The8BitEnthusiast/apple-1-breadboard/schematics/aci.kicad_sch

## KiCad design schematics/aci.kicad_sch (2024-11-09, an earlier design)

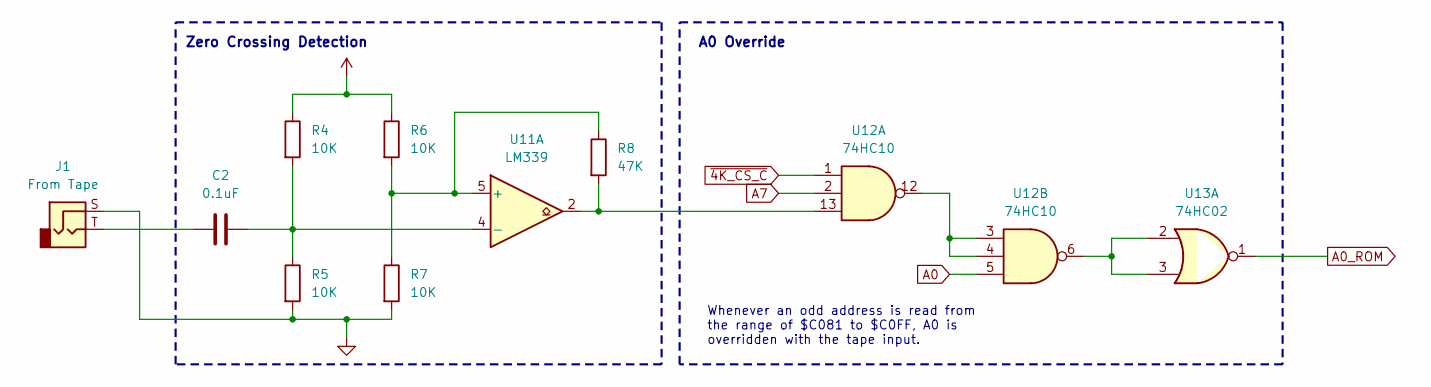
[picture p7: schematic aci.kicad_sch]

Parts:
C2: 0.1uF
J1: From Tape
R4, R5, R6, R7: 10K
R8: 47K
U11: LM339
U12: 74HC10
U13: 74HC02

Connections:
A0: U12.5
A0_ROM: U13.1
A7: U12.2
GND: J1.S, R5.2, R7.2
unnamed: C2.1, J1.T
unnamed: C2.2, R4.2, R5.1, U11.4 (-)
unnamed: R6.2, R7.1, R8.1, U11.5 (+)
unnamed: R8.2, U11.2, U12.13
unnamed: U12.6, U13.2, U13.3
unnamed: U12.3, U12.4, U12.12
VCC: R4.1, R6.1
~4K_CS_C: U12.1

Notes on the sheet:
A0 Override
Whenever an odd address is read from the range of $C081 to $C0FF, A0 is overridden with the tape input.
Zero Crossing Detection
