The8BitEnthusiast/apple-1-breadboard/schematics/apple-1.kicad_sch

## KiCad design schematics/apple-1.kicad_sch (2025-04-07, an earlier design)

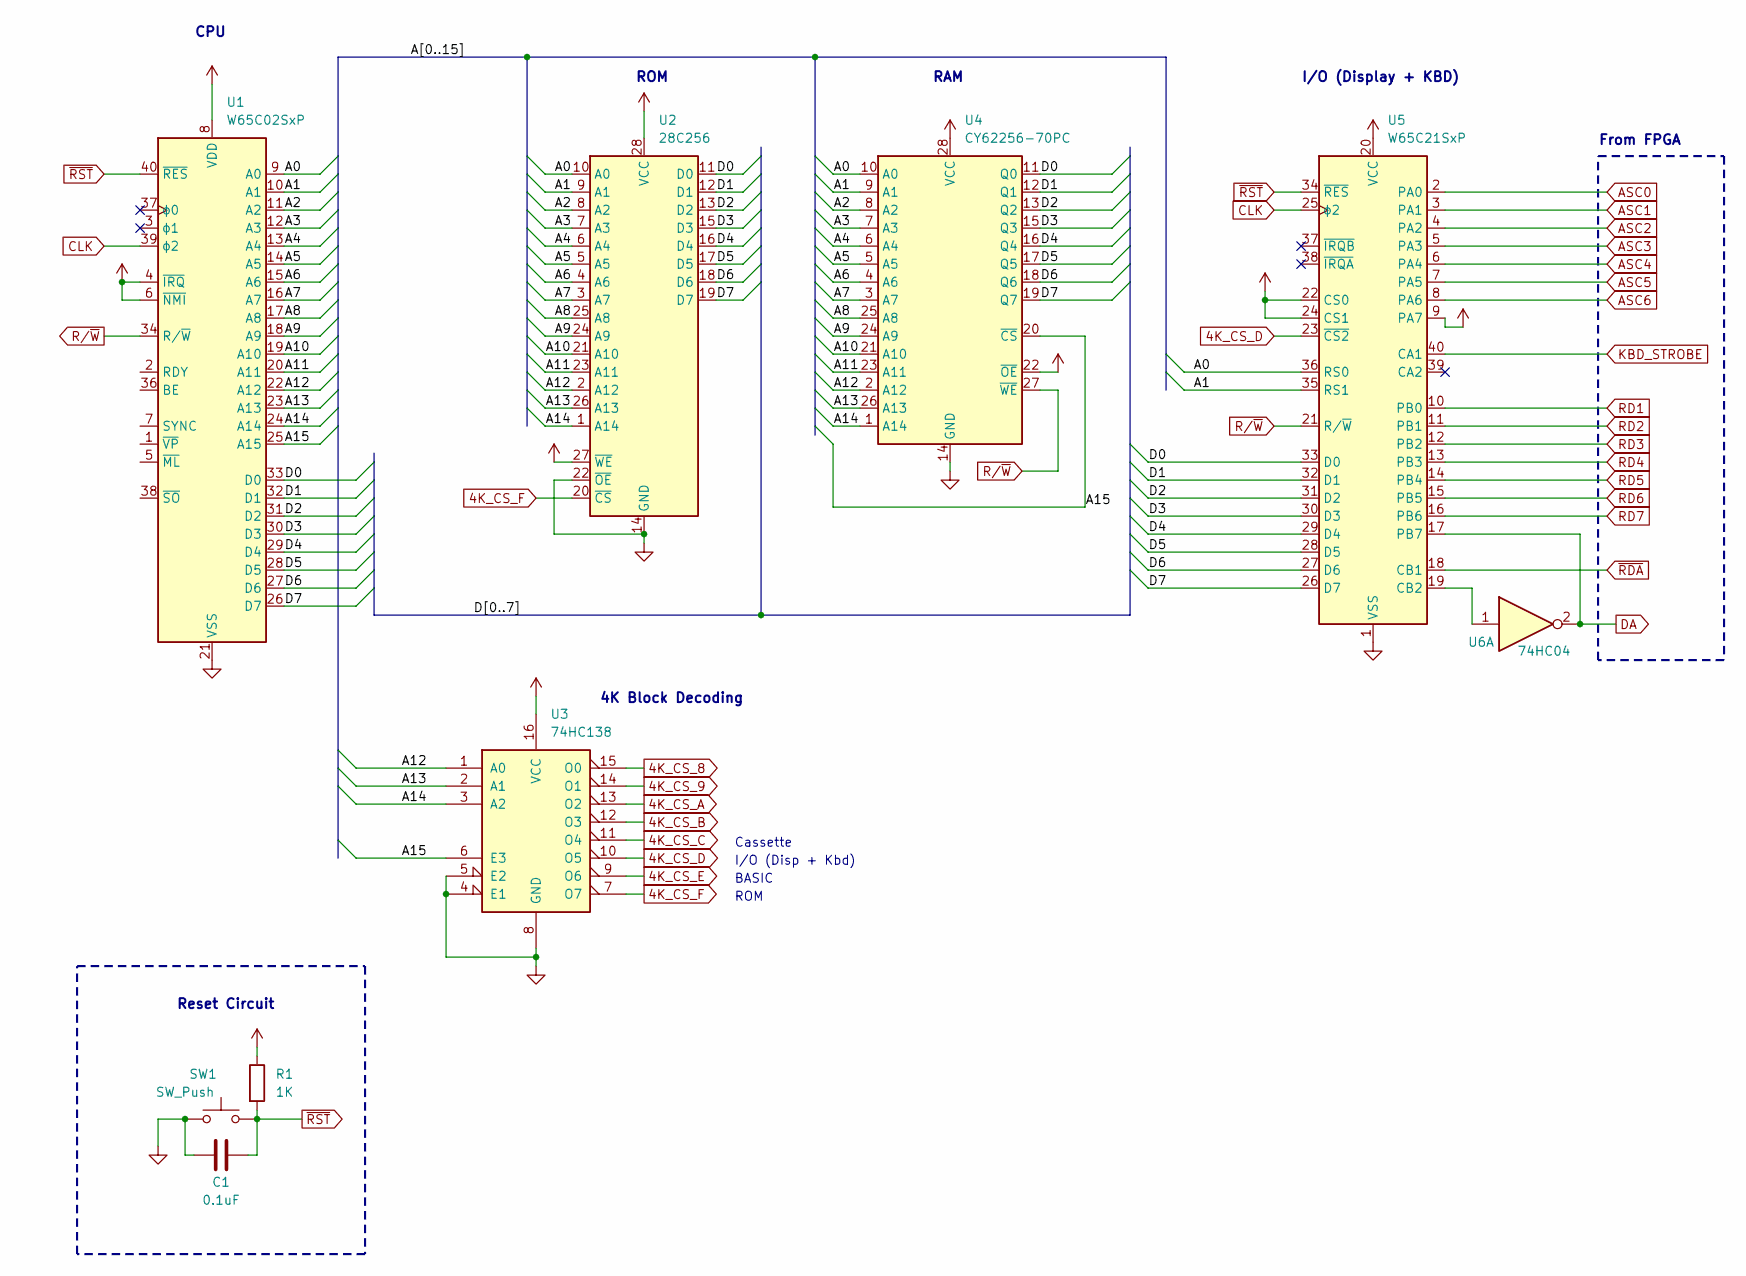
[picture p8: schematic apple-1.kicad_sch]

Parts:
C1: 0.1uF
R1: 1K
SW1: SW_Push
U1: W65C02SxP; DIP-40_W15.24mm
U2: 28C256
U3: 74HC138
U4: CY62256-70PC; DIP-28_W15.24mm
U5: W65C21SxP; DIP-40_W15.24mm
U6: 74HC04

Connections:
4K_CS_8: U3.15 (O0)
4K_CS_9: U3.14 (O1)
4K_CS_A: U3.13 (O2)
4K_CS_B: U3.12 (O3)
4K_CS_C: U3.11 (O4)
4K_CS_D: U3.10 (O5), U5.23 (~CS2)
4K_CS_E: U3.9 (O6)
4K_CS_F: U2.20 (~CS), U3.7 (O7)
A0: U1.9 (A0), U2.10 (A0), U4.10 (A0), U5.36 (RS0)
A1: U1.10 (A1), U2.9 (A1), U4.9 (A1), U5.35 (RS1)
A2: U1.11 (A2), U2.8 (A2), U4.8 (A2)
A3: U1.12 (A3), U2.7 (A3), U4.7 (A3)
A4: U1.13 (A4), U2.6 (A4), U4.6 (A4)
A5: U1.14 (A5), U2.5 (A5), U4.5 (A5)
A6: U1.15 (A6), U2.4 (A6), U4.4 (A6)
A7: U1.16 (A7), U2.3 (A7), U4.3 (A7)
A8: U1.17 (A8), U2.25 (A8), U4.25 (A8)
A9: U1.18 (A9), U2.24 (A9), U4.24 (A9)
A10: U1.19 (A10), U2.21 (A10), U4.21 (A10)
A11: U1.20 (A11), U2.23 (A11), U4.23 (A11)
A12: U1.22 (A12), U2.2 (A12), U3.1 (A0), U4.2 (A12)
A13: U1.23 (A13), U2.26 (A13), U3.2 (A1), U4.26 (A13)
A14: U1.24 (A14), U2.1 (A14), U3.3 (A2), U4.1 (A14)
A15: U1.25 (A15), U3.6 (E3), U4.20 (~CS)
ASC0: U5.2 (PA0)
ASC1: U5.3 (PA1)
ASC2: U5.4 (PA2)
ASC3: U5.5 (PA3)
ASC4: U5.6 (PA4)
ASC5: U5.7 (PA5)
ASC6: U5.8 (PA6)
CLK: U1.39 (ϕ2), U5.25 (ϕ2)
D0: U1.33 (D0), U2.11 (D0), U4.11 (Q0), U5.33 (D0)
D1: U1.32 (D1), U2.12 (D1), U4.12 (Q1), U5.32 (D1)
D2: U1.31 (D2), U2.13 (D2), U4.13 (Q2), U5.31 (D2)
D3: U1.30 (D3), U2.15 (D3), U4.15 (Q3), U5.30 (D3)
D4: U1.29 (D4), U2.16 (D4), U4.16 (Q4), U5.29 (D4)
D5: U1.28 (D5), U2.17 (D5), U4.17 (Q5), U5.28 (D5)
D6: U1.27 (D6), U2.18 (D6), U4.18 (Q6), U5.27 (D6)
D7: U1.26 (D7), U2.19 (D7), U4.19 (Q7), U5.26 (D7)
DA: U5.17 (PB7), U6.2
GND: C1.2, SW1.1, U1.21 (VSS), U2.14 (GND), U2.22 (~OE), U3.4 (E1), U3.5 (E2), U3.8 (GND), U4.14 (GND), U5.1 (VSS)
KBD_STROBE: U5.40 (CA1)
unnamed: U5.19 (CB2), U6.1
RD1: U5.10 (PB0)
RD2: U5.11 (PB1)
RD3: U5.12 (PB2)
RD4: U5.13 (PB3)
RD5: U5.14 (PB4)
RD6: U5.15 (PB5)
RD7: U5.16 (PB6)
R/~W: U1.34 (R/~W), U4.27 (~WE), U5.21 (R/~W)
VCC: R1.1, U1.4 (~IRQ), U1.6 (~NMI), U1.8 (VDD), U2.27 (~WE), U2.28 (VCC), U3.16 (VCC), U4.22 (~OE), U4.28 (VCC), U5.9 (PA7), U5.20 (VCC), U5.22 (CS0), U5.24 (CS1)
~RDA: U5.18 (CB1)
~RST: C1.1, R1.2, SW1.2, U1.40 (~RES), U5.34 (~RES)

Notes on the sheet:
BASIC
ROM
I/O (Disp + Kbd)
4K Block Decoding
Cassette
RAM
Reset Circuit
From FPGA
CPU
I/O (Display + KBD)
