The8BitEnthusiast/apple-1-breadboard/schematics/uart.kicad_sch

## KiCad design schematics/uart.kicad_sch (2025-04-07, an earlier design)

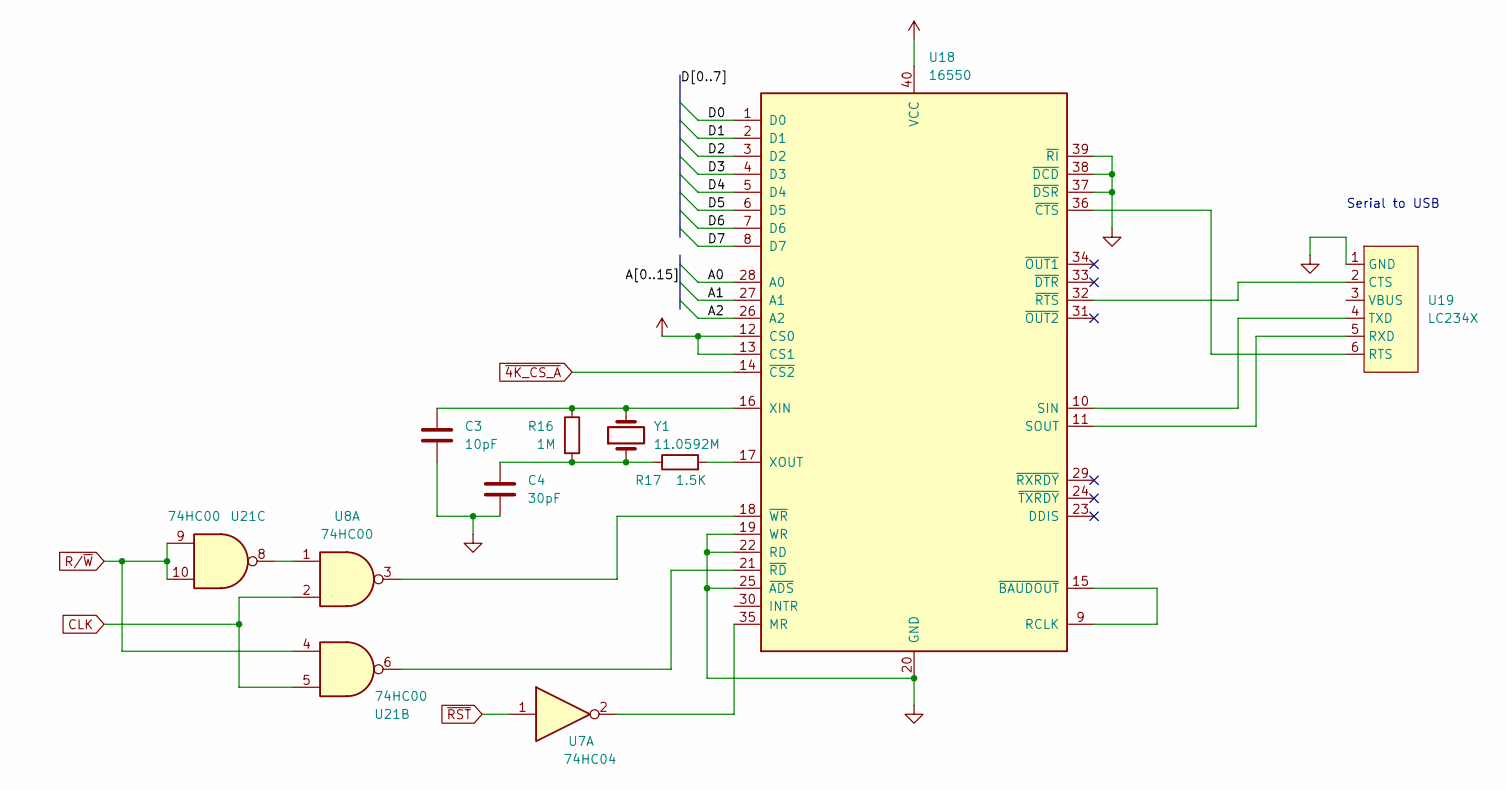
[picture p10: schematic uart.kicad_sch]

Parts:
C3: 10pF
C4: 30pF
R16: 1M
R17: 1.5K
U7: 74HC04
U8, U21: 74HC00
U18: 16550; DIP-40_W15.24mm
U19: LC234X
Y1: 11.0592M

Connections:
A0: U18.28 (A0)
A1: U18.27 (A1)
A2: U18.26 (A2)
CLK: U8.2, U21.5
D0: U18.1 (D0)
D1: U18.2 (D1)
D2: U18.3 (D2)
D3: U18.4 (D3)
D4: U18.5 (D4)
D5: U18.6 (D5)
D6: U18.7 (D6)
D7: U18.8 (D7)
GND: C3.2, C4.2, U18.19 (WR), U18.20 (GND), U18.22 (RD), U18.25 (~ADS), U18.37 (~DSR), U18.38 (~DCD), U18.39 (~RI), U19.1 (GND)
unnamed: C3.1, R16.1, U18.16 (XIN), Y1.2
unnamed: C4.1, R16.2, R17.1, Y1.1
unnamed: R17.2, U18.17 (XOUT)
unnamed: U18.10 (SIN), U19.4 (TXD)
unnamed: U18.11 (SOUT), U19.5 (RXD)
unnamed: U18.9 (RCLK), U18.15 (~BAUDOUT)
unnamed: U8.3, U18.18 (~WR)
unnamed: U18.21 (~RD), U21.6
unnamed: U18.32 (~RTS), U19.2 (CTS)
unnamed: U7.2, U18.35 (MR)
unnamed: U18.36 (~CTS), U19.6 (RTS)
unnamed: U8.1, U21.8
R/~W: U21.4, U21.9, U21.10
VCC: U18.12 (CS0), U18.13 (CS1), U18.40 (VCC)
~4K_CS_A: U18.14 (~CS2)
~RST: U7.1

Notes on the sheet:
Serial to USB
