The8BitEnthusiast/apple-1-breadboard/src/hdl/ice40-clk-gen/pll_12_29.v

/**
 * PLL configuration
 *
 * This Verilog module was generated automatically
 * using the icepll tool from the IceStorm project.
 * Use at your own risk.
 *
 * Given input frequency:        12.000 MHz
 * Requested output frequency:   28.636 MHz
 * Achieved output frequency:    28.500 MHz
 */

module pll_12_29(
	input  clock_in,
	output clock_out,
	output locked
	);

SB_PLL40_PAD #(
		.FEEDBACK_PATH("SIMPLE"),
		.DIVR(4'b0000),		// DIVR =  0
		.DIVF(7'b1001011),	// DIVF = 75
		.DIVQ(3'b101),		// DIVQ =  5
		.FILTER_RANGE(3'b001)	// FILTER_RANGE = 1
	) uut (
		.LOCK(locked),
		.RESETB(1'b1),
		.BYPASS(1'b0),
		.PACKAGEPIN(clock_in),
		.PLLOUTCORE(clock_out)
		);

endmodule
