The8BitEnthusiast/apple-1-breadboard/ip/clk_gen/clk_gen_stub.v

// Copyright 1986-2022 Xilinx, Inc. All Rights Reserved.
// --------------------------------------------------------------------------------
// Tool Version: Vivado v.2022.2 (lin64) Build 3671981 Fri Oct 14 04:59:54 MDT 2022
// Date        : Mon Feb 13 12:19:39 2023
// Host        : spock running 64-bit Ubuntu 22.04.1 LTS
// Command     : write_verilog -force -mode synth_stub
//               /home/steeve/projects/apple-1-video-terminal-on-fpga/ip/clk_gen/clk_gen_stub.v
// Design      : clk_gen
// Purpose     : Stub declaration of top-level module interface
// Device      : xc7a35tftg256-1
// --------------------------------------------------------------------------------

// This empty module with port declaration file causes synthesis tools to infer a black box for IP.
// The synthesis directives are for Synopsys Synplify support to prevent IO buffer insertion.
// Please paste the declaration into a Verilog source file or add the file as an additional source.
module clk_gen(clk_out, locked, clk_in)
/* synthesis syn_black_box black_box_pad_pin="clk_out,locked,clk_in" */;
  output clk_out;
  output locked;
  input clk_in;
endmodule
